zrrraa/X-Focus/dependencies/images/login_1.png

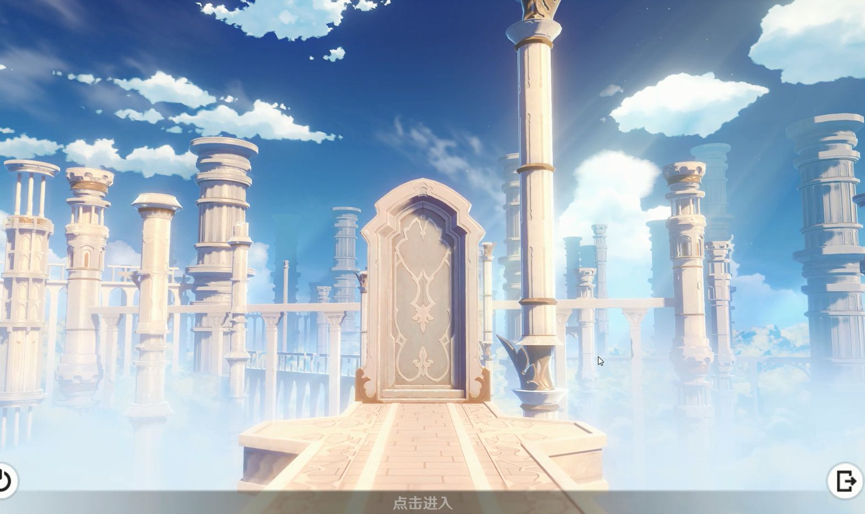
dependencies/images/login_1.png
