zrrraa/X-Focus/dependencies/images/lzt1_touxiang.png

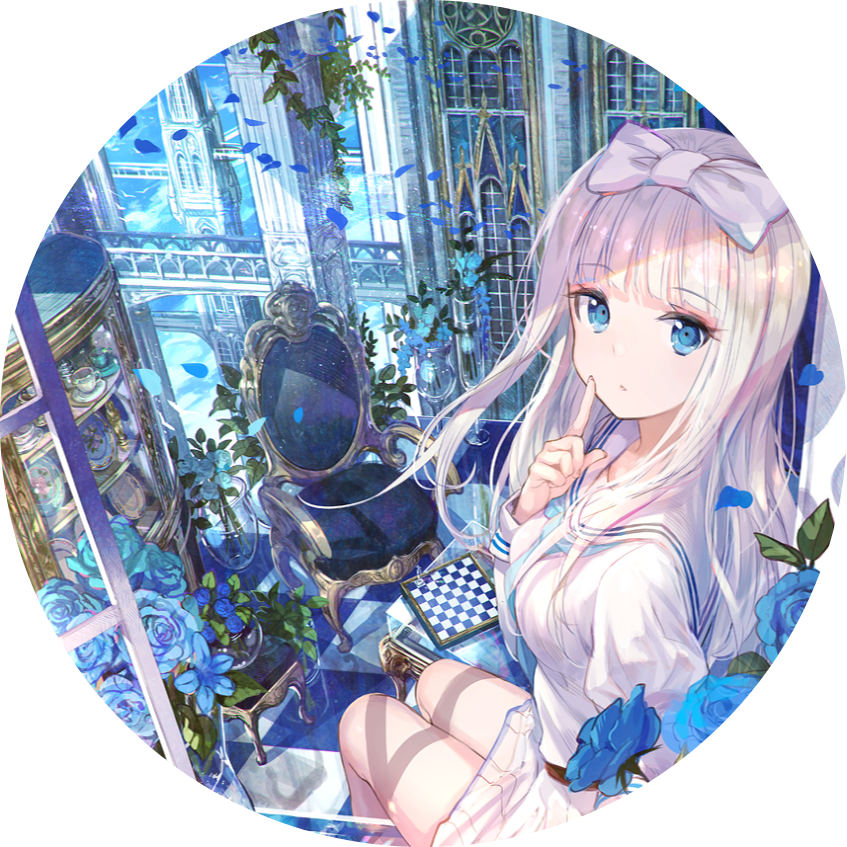
dependencies/images/lzt1_touxiang.png
