zrrraa/X-Focus/dependencies/images/signup.jpg

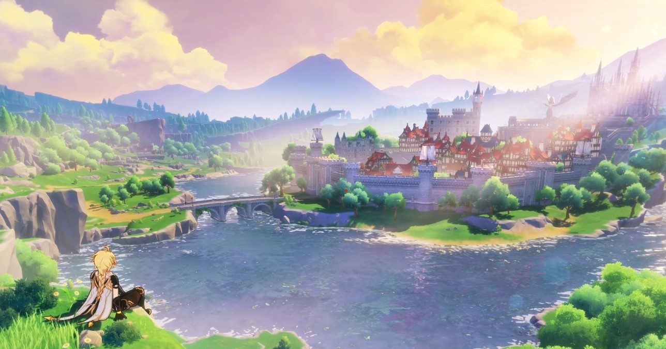
dependencies/images/signup.jpg
