zrrraa/X-Focus/dependencies/images/zrraaa_touxiang.png

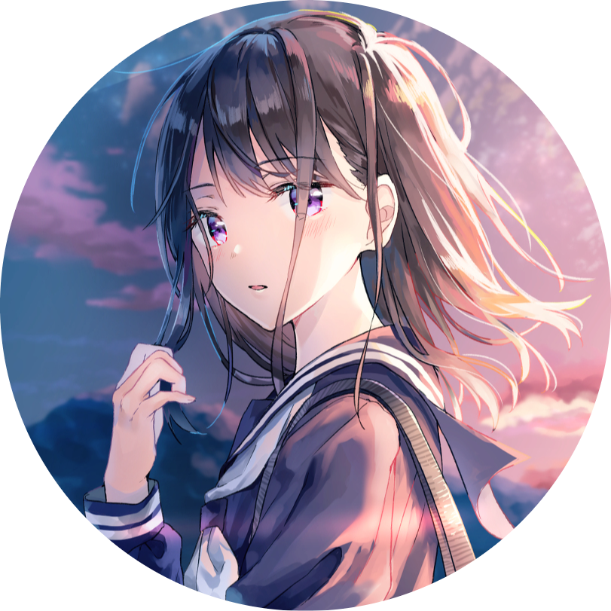
dependencies/images/zrraaa_touxiang.png
