zrrraa/X-Focus/SVMImageClassification/photo2/0/0.jpg

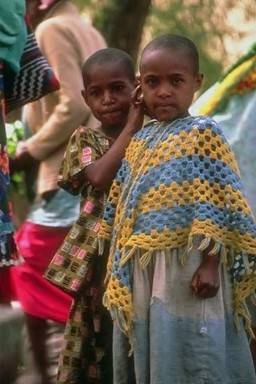
SVMImageClassification/photo2/0/0.jpg
