zrrraa/X-Focus/SVMImageClassification/photo2/0/3.jpg

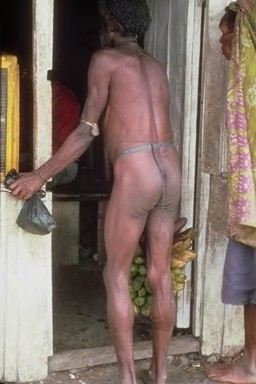
SVMImageClassification/photo2/0/3.jpg
