zrrraa/X-Focus/SVMImageClassification/photo2/0/6.jpg

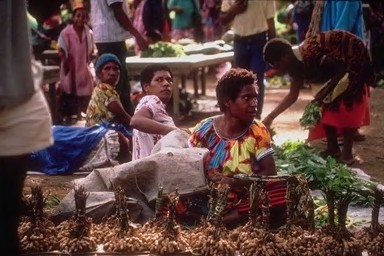
SVMImageClassification/photo2/0/6.jpg
