zrrraa/X-Focus/SVMImageClassification/photo2/0/7.jpg

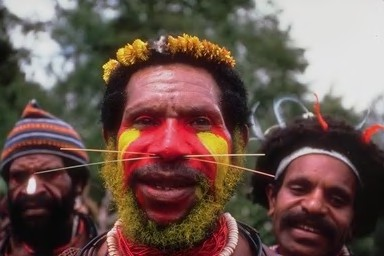
SVMImageClassification/photo2/0/7.jpg
