zrrraa/X-Focus/SVMImageClassification/photo2/0/9.jpg

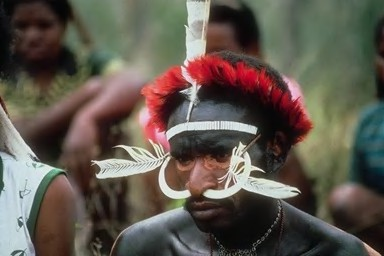
SVMImageClassification/photo2/0/9.jpg
