zrrraa/X-Focus/SVMImageClassification/photo2/0/15.jpg

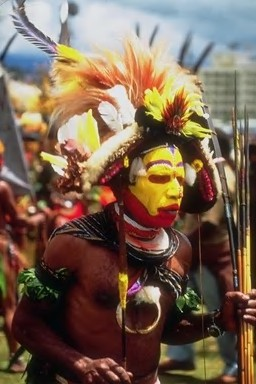
SVMImageClassification/photo2/0/15.jpg
