zrrraa/X-Focus/SVMImageClassification/photo2/0/25.jpg

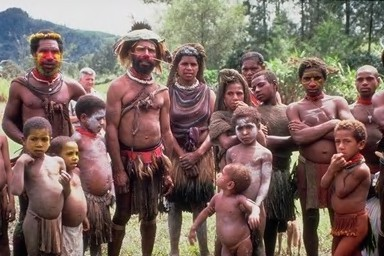
SVMImageClassification/photo2/0/25.jpg
