zrrraa/X-Focus/SVMImageClassification/photo2/0/32.jpg

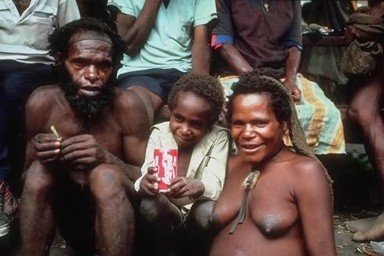
SVMImageClassification/photo2/0/32.jpg
