zrrraa/X-Focus/SVMImageClassification/photo2/0/33.jpg

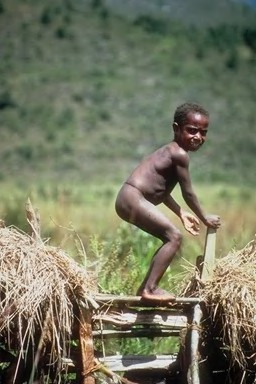
SVMImageClassification/photo2/0/33.jpg
