zrrraa/X-Focus/SVMImageClassification/photo2/0/38.jpg

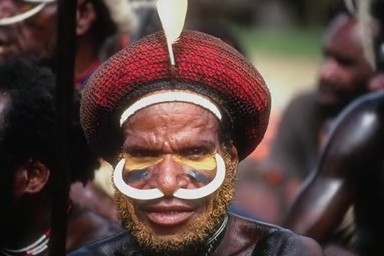
SVMImageClassification/photo2/0/38.jpg
