zrrraa/X-Focus/SVMImageClassification/photo2/0/42.jpg

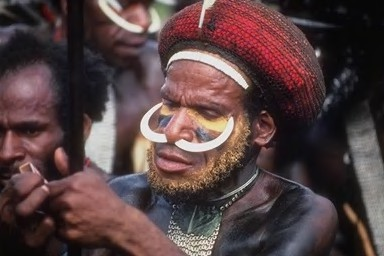
SVMImageClassification/photo2/0/42.jpg
