zrrraa/X-Focus/SVMImageClassification/photo2/0/44.jpg

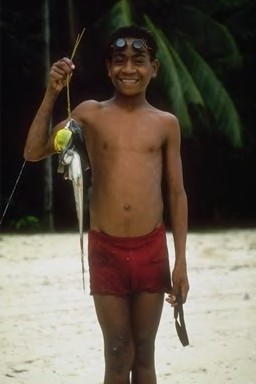
SVMImageClassification/photo2/0/44.jpg
