zrrraa/X-Focus/SVMImageClassification/photo2/0/46.jpg

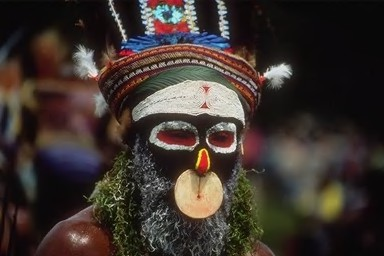
SVMImageClassification/photo2/0/46.jpg
