zrrraa/X-Focus/SVMImageClassification/photo2/0/49.jpg

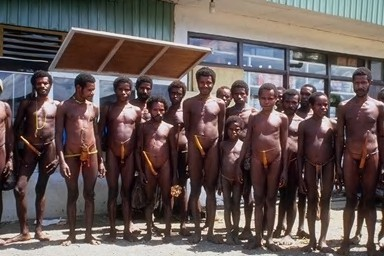
SVMImageClassification/photo2/0/49.jpg
