zrrraa/X-Focus/SVMImageClassification/photo2/0/62.jpg

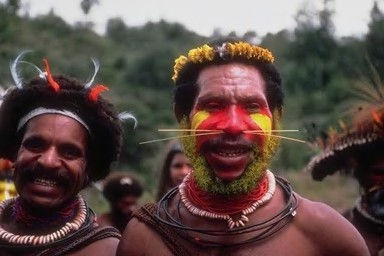
SVMImageClassification/photo2/0/62.jpg
