zrrraa/X-Focus/SVMImageClassification/photo2/0/65.jpg

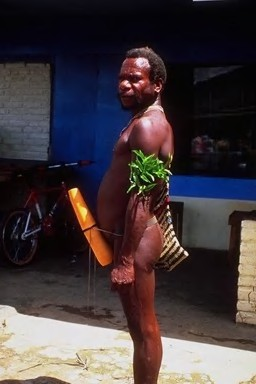
SVMImageClassification/photo2/0/65.jpg
