zrrraa/X-Focus/SVMImageClassification/photo2/0/79.jpg

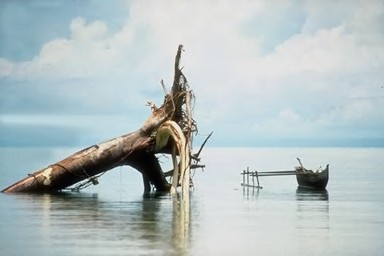
SVMImageClassification/photo2/0/79.jpg
