zrrraa/X-Focus/SVMImageClassification/photo2/0/83.jpg

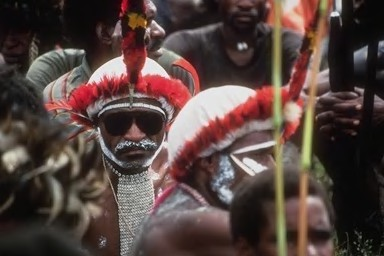
SVMImageClassification/photo2/0/83.jpg
