zrrraa/X-Focus/SVMImageClassification/photo2/0/86.jpg

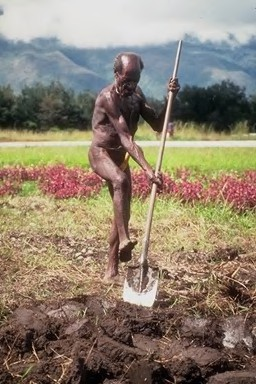
SVMImageClassification/photo2/0/86.jpg
