zrrraa/X-Focus/SVMImageClassification/photo2/0/90.jpg

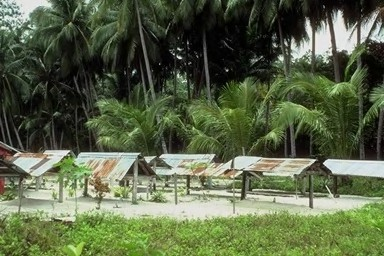
SVMImageClassification/photo2/0/90.jpg
