zrrraa/X-Focus/SVMImageClassification/photo2/0/97.jpg

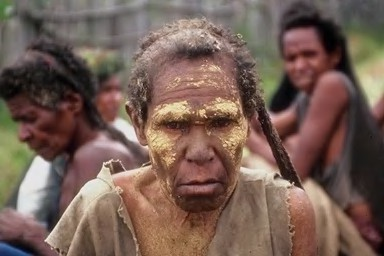
SVMImageClassification/photo2/0/97.jpg
