zrrraa/X-Focus/SVMImageClassification/photo2/1/100.jpg

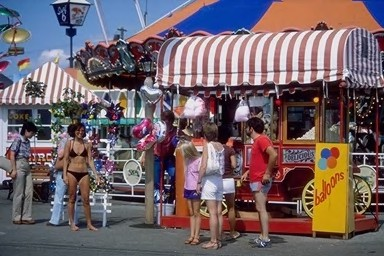
SVMImageClassification/photo2/1/100.jpg
