zrrraa/X-Focus/SVMImageClassification/photo2/1/103.jpg

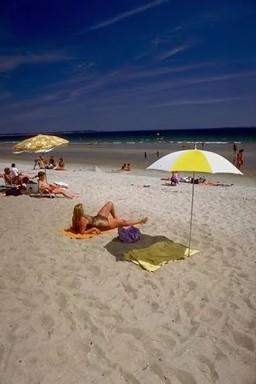
SVMImageClassification/photo2/1/103.jpg
