zrrraa/X-Focus/SVMImageClassification/photo2/1/105.jpg

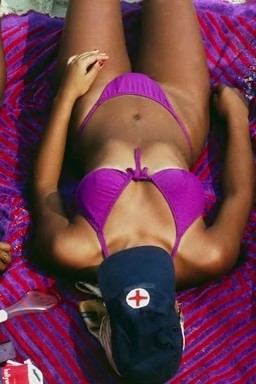
SVMImageClassification/photo2/1/105.jpg
