zrrraa/X-Focus/SVMImageClassification/photo2/1/115.jpg

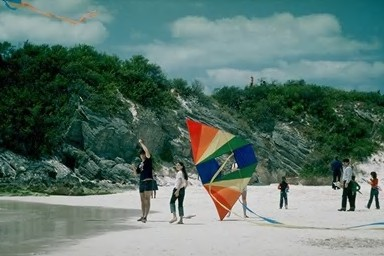
SVMImageClassification/photo2/1/115.jpg
