zrrraa/X-Focus/SVMImageClassification/photo2/1/118.jpg

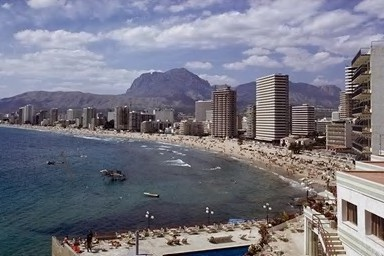
SVMImageClassification/photo2/1/118.jpg
