zrrraa/X-Focus/SVMImageClassification/photo2/1/129.jpg

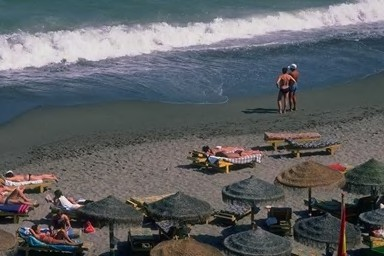
SVMImageClassification/photo2/1/129.jpg
