zrrraa/X-Focus/SVMImageClassification/photo2/1/141.jpg

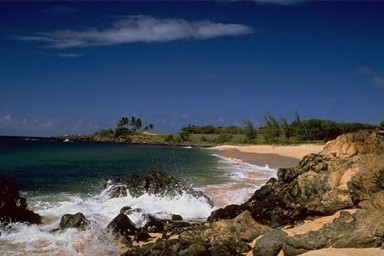
SVMImageClassification/photo2/1/141.jpg
