zrrraa/X-Focus/SVMImageClassification/photo2/1/146.jpg

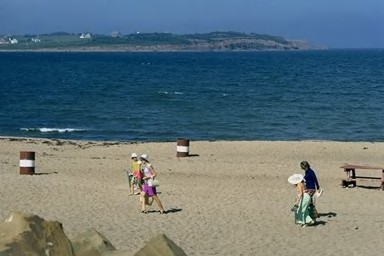
SVMImageClassification/photo2/1/146.jpg
