zrrraa/X-Focus/SVMImageClassification/photo2/1/149.jpg

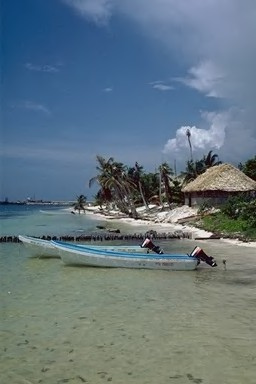
SVMImageClassification/photo2/1/149.jpg
