zrrraa/X-Focus/SVMImageClassification/photo2/1/160.jpg

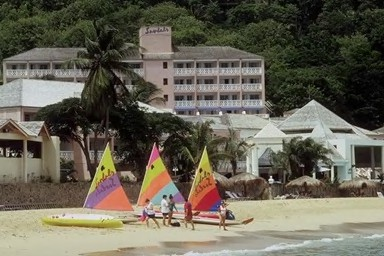
SVMImageClassification/photo2/1/160.jpg
