zrrraa/X-Focus/SVMImageClassification/photo2/1/161.jpg

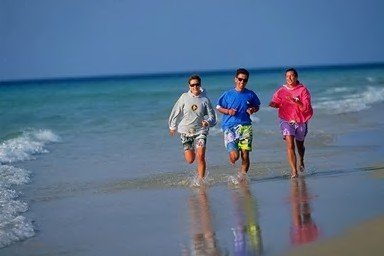
SVMImageClassification/photo2/1/161.jpg
