zrrraa/X-Focus/SVMImageClassification/photo2/1/162.jpg

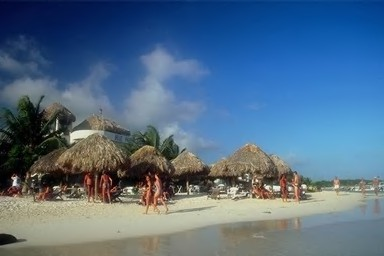
SVMImageClassification/photo2/1/162.jpg
