zrrraa/X-Focus/SVMImageClassification/photo2/1/167.jpg

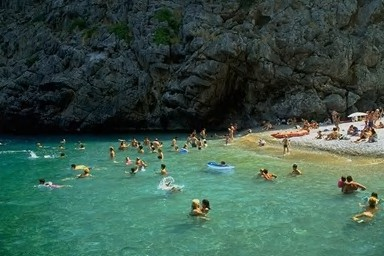
SVMImageClassification/photo2/1/167.jpg
