zrrraa/X-Focus/SVMImageClassification/photo2/1/170.jpg

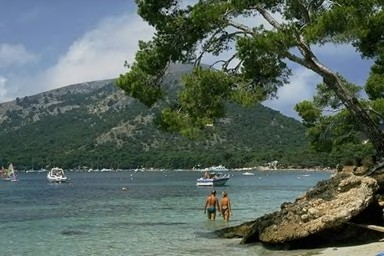
SVMImageClassification/photo2/1/170.jpg
