zrrraa/X-Focus/SVMImageClassification/photo2/1/172.jpg

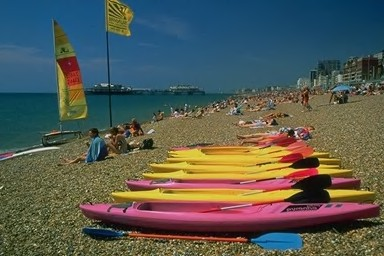
SVMImageClassification/photo2/1/172.jpg
