zrrraa/X-Focus/SVMImageClassification/photo2/1/175.jpg

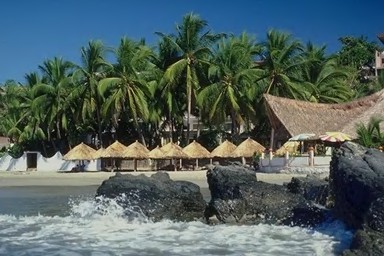
SVMImageClassification/photo2/1/175.jpg
