zrrraa/X-Focus/SVMImageClassification/photo2/1/178.jpg

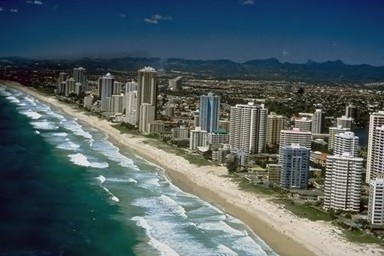
SVMImageClassification/photo2/1/178.jpg
