zrrraa/X-Focus/SVMImageClassification/photo2/1/180.jpg

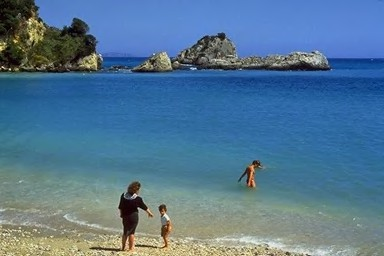
SVMImageClassification/photo2/1/180.jpg
