zrrraa/X-Focus/SVMImageClassification/photo2/1/187.jpg

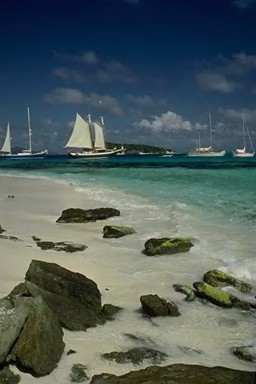
SVMImageClassification/photo2/1/187.jpg
