zrrraa/X-Focus/SVMImageClassification/photo2/1/194.jpg

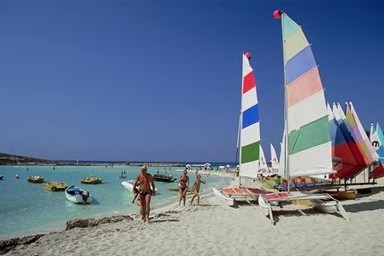
SVMImageClassification/photo2/1/194.jpg
