zrrraa/X-Focus/SVMImageClassification/photo2/2/202.jpg

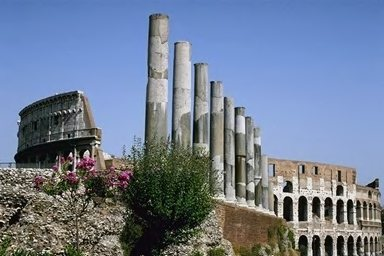
SVMImageClassification/photo2/2/202.jpg
