zrrraa/X-Focus/SVMImageClassification/photo2/2/207.jpg

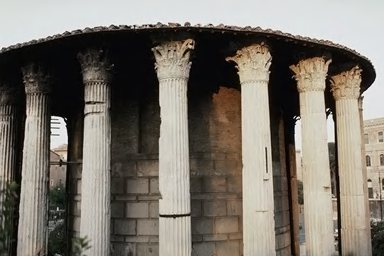
SVMImageClassification/photo2/2/207.jpg
