zrrraa/X-Focus/SVMImageClassification/photo2/2/211.jpg

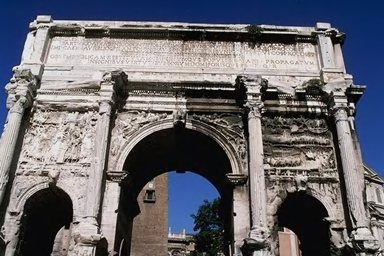
SVMImageClassification/photo2/2/211.jpg
