zrrraa/X-Focus/SVMImageClassification/photo2/2/225.jpg

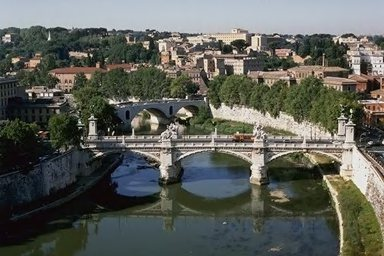
SVMImageClassification/photo2/2/225.jpg
