zrrraa/X-Focus/SVMImageClassification/photo2/2/231.jpg

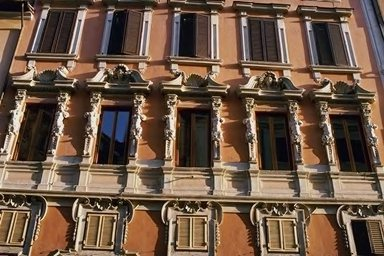
SVMImageClassification/photo2/2/231.jpg
