zrrraa/X-Focus/SVMImageClassification/photo2/2/239.jpg

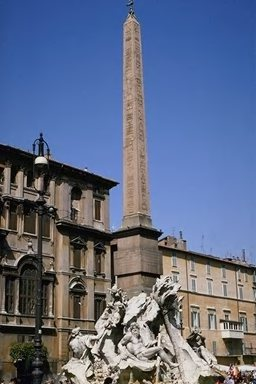
SVMImageClassification/photo2/2/239.jpg
