zrrraa/X-Focus/SVMImageClassification/photo2/2/246.jpg

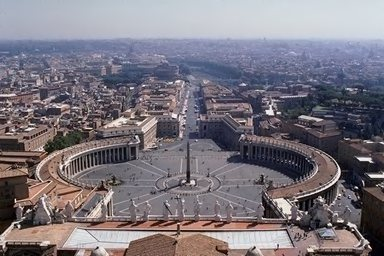
SVMImageClassification/photo2/2/246.jpg
