zrrraa/X-Focus/SVMImageClassification/photo2/2/264.jpg

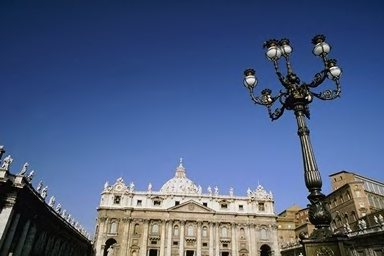
SVMImageClassification/photo2/2/264.jpg
