zrrraa/X-Focus/SVMImageClassification/photo2/2/267.jpg

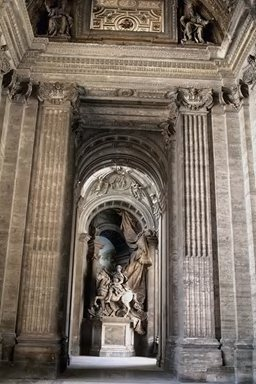
SVMImageClassification/photo2/2/267.jpg
