zrrraa/X-Focus/SVMImageClassification/photo2/2/278.jpg

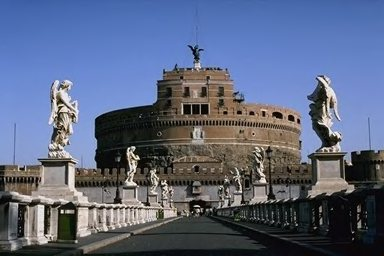
SVMImageClassification/photo2/2/278.jpg
