zrrraa/X-Focus/SVMImageClassification/photo2/3/300.jpg

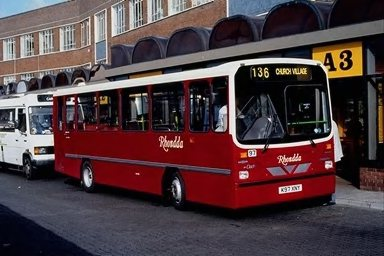
SVMImageClassification/photo2/3/300.jpg
