zrrraa/X-Focus/SVMImageClassification/photo2/3/312.jpg

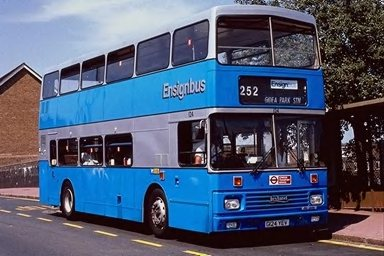
SVMImageClassification/photo2/3/312.jpg
