zrrraa/X-Focus/SVMImageClassification/photo2/3/313.jpg

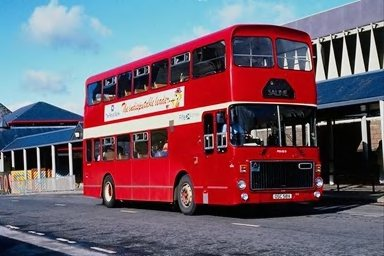
SVMImageClassification/photo2/3/313.jpg
