zrrraa/X-Focus/SVMImageClassification/photo2/3/318.jpg

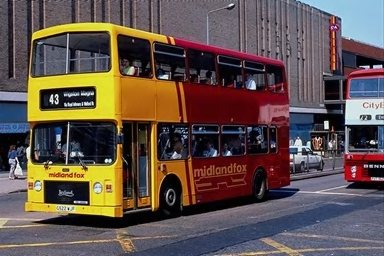
SVMImageClassification/photo2/3/318.jpg
