zrrraa/X-Focus/SVMImageClassification/photo2/3/319.jpg

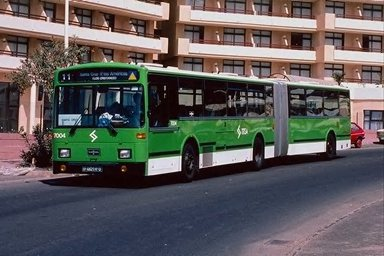
SVMImageClassification/photo2/3/319.jpg
