zrrraa/X-Focus/SVMImageClassification/photo2/3/320.jpg

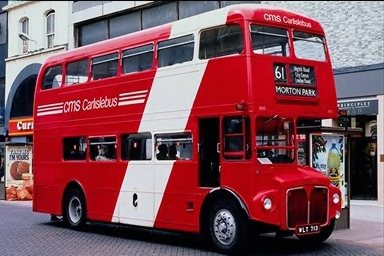
SVMImageClassification/photo2/3/320.jpg
