zrrraa/X-Focus/SVMImageClassification/photo2/3/337.jpg

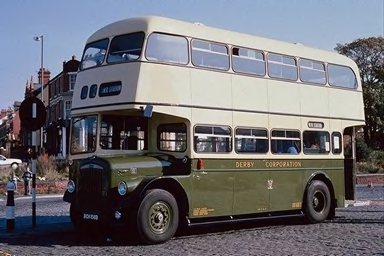
SVMImageClassification/photo2/3/337.jpg
