zrrraa/X-Focus/SVMImageClassification/photo2/3/340.jpg

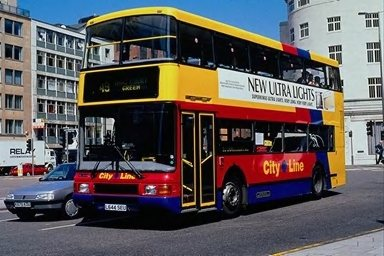
SVMImageClassification/photo2/3/340.jpg
