zrrraa/X-Focus/SVMImageClassification/photo2/3/342.jpg

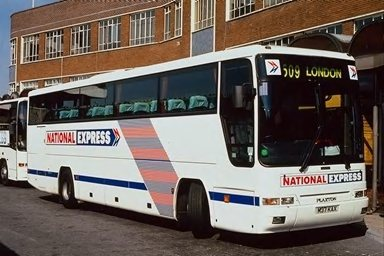
SVMImageClassification/photo2/3/342.jpg
