zrrraa/X-Focus/SVMImageClassification/photo2/3/356.jpg

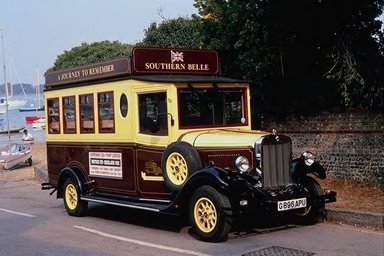
SVMImageClassification/photo2/3/356.jpg
