zrrraa/X-Focus/SVMImageClassification/photo2/3/363.jpg

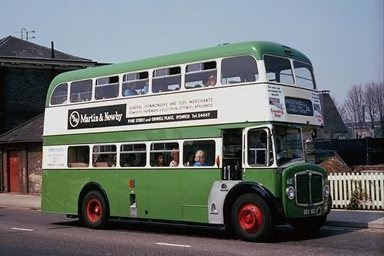
SVMImageClassification/photo2/3/363.jpg
