zrrraa/X-Focus/SVMImageClassification/photo2/3/382.jpg

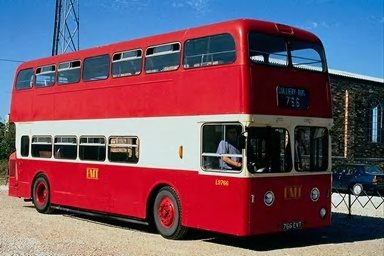
SVMImageClassification/photo2/3/382.jpg
