zrrraa/X-Focus/SVMImageClassification/photo2/3/388.jpg

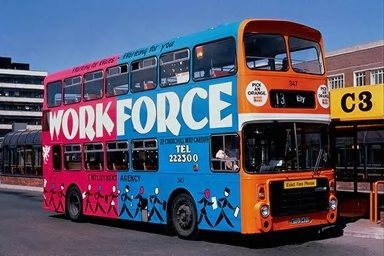
SVMImageClassification/photo2/3/388.jpg
