zrrraa/X-Focus/SVMImageClassification/photo2/3/393.jpg

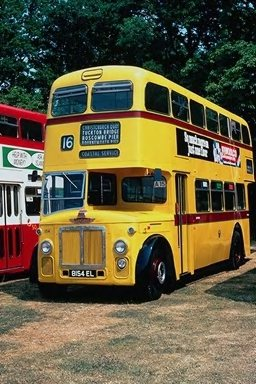
SVMImageClassification/photo2/3/393.jpg
