zrrraa/X-Focus/SVMImageClassification/photo2/4/403.jpg

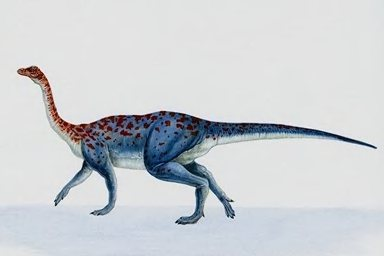
SVMImageClassification/photo2/4/403.jpg
