zrrraa/X-Focus/SVMImageClassification/photo2/4/406.jpg

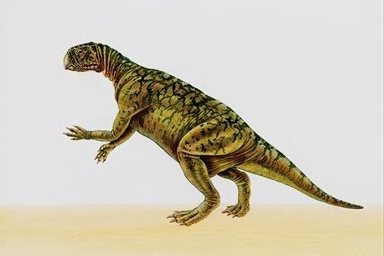
SVMImageClassification/photo2/4/406.jpg
