zrrraa/X-Focus/SVMImageClassification/photo2/4/411.jpg

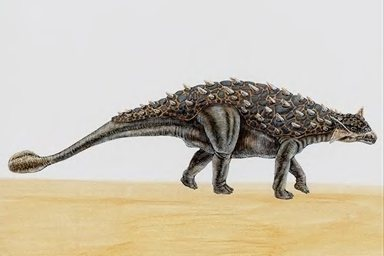
SVMImageClassification/photo2/4/411.jpg
