zrrraa/X-Focus/SVMImageClassification/photo2/4/413.jpg

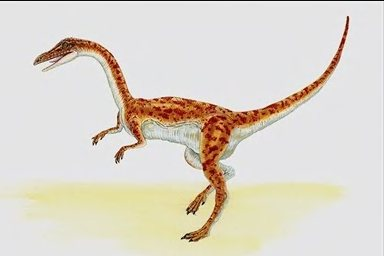
SVMImageClassification/photo2/4/413.jpg
