zrrraa/X-Focus/SVMImageClassification/photo2/4/423.jpg

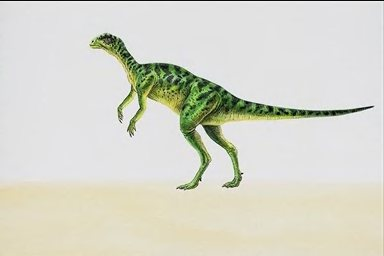
SVMImageClassification/photo2/4/423.jpg
