zrrraa/X-Focus/SVMImageClassification/photo2/4/424.jpg

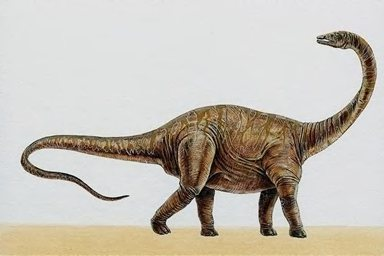
SVMImageClassification/photo2/4/424.jpg
