zrrraa/X-Focus/SVMImageClassification/photo2/4/426.jpg

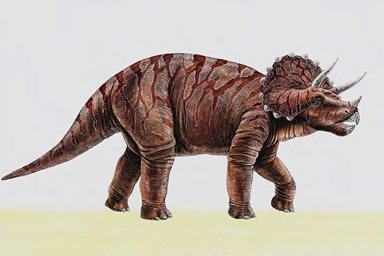
SVMImageClassification/photo2/4/426.jpg
