zrrraa/X-Focus/SVMImageClassification/photo2/4/437.jpg

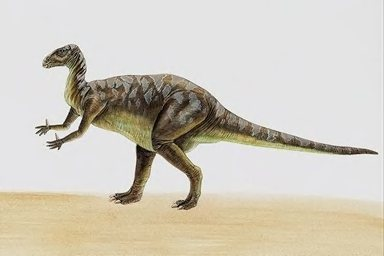
SVMImageClassification/photo2/4/437.jpg
