zrrraa/X-Focus/SVMImageClassification/photo2/4/442.jpg

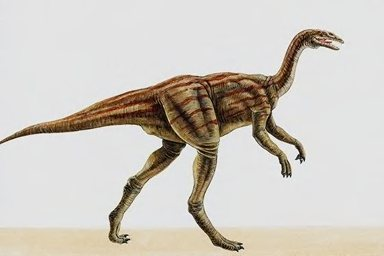
SVMImageClassification/photo2/4/442.jpg
