zrrraa/X-Focus/SVMImageClassification/photo2/4/444.jpg

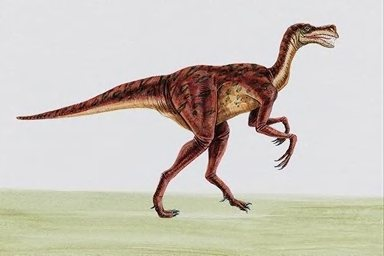
SVMImageClassification/photo2/4/444.jpg
