zrrraa/X-Focus/SVMImageClassification/photo2/4/446.jpg

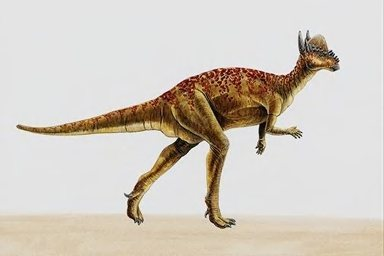
SVMImageClassification/photo2/4/446.jpg
