zrrraa/X-Focus/SVMImageClassification/photo2/4/447.jpg

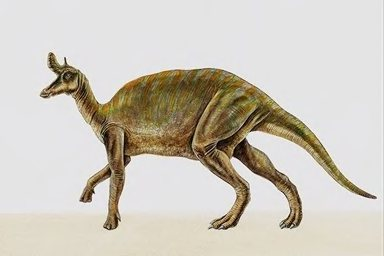
SVMImageClassification/photo2/4/447.jpg
