zrrraa/X-Focus/SVMImageClassification/photo2/4/449.jpg

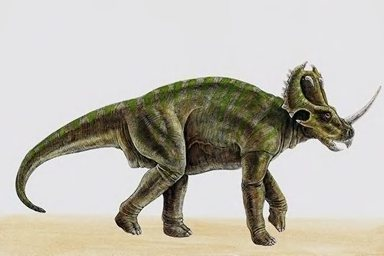
SVMImageClassification/photo2/4/449.jpg
