zrrraa/X-Focus/SVMImageClassification/photo2/4/460.jpg

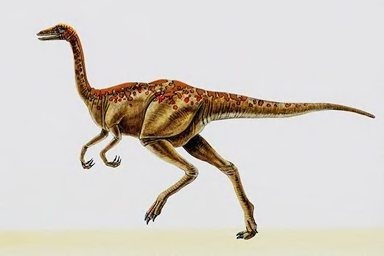
SVMImageClassification/photo2/4/460.jpg
