zrrraa/X-Focus/SVMImageClassification/photo2/4/462.jpg

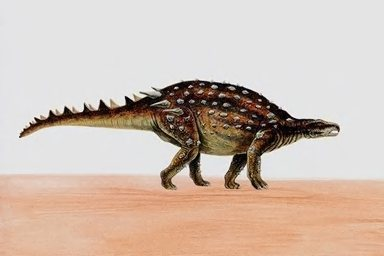
SVMImageClassification/photo2/4/462.jpg
