zrrraa/X-Focus/SVMImageClassification/photo2/4/463.jpg

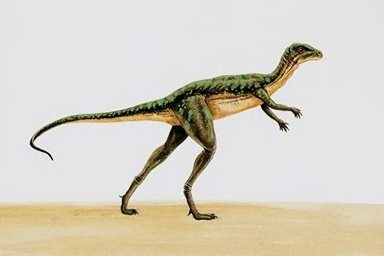
SVMImageClassification/photo2/4/463.jpg
