zrrraa/X-Focus/SVMImageClassification/photo2/4/467.jpg

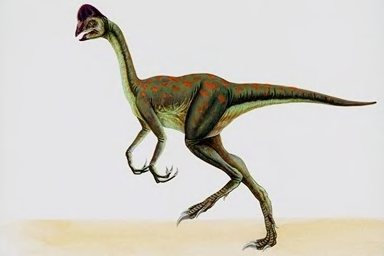
SVMImageClassification/photo2/4/467.jpg
