zrrraa/X-Focus/SVMImageClassification/photo2/4/475.jpg

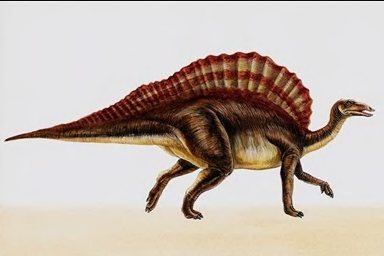
SVMImageClassification/photo2/4/475.jpg
