zrrraa/X-Focus/SVMImageClassification/photo2/4/477.jpg

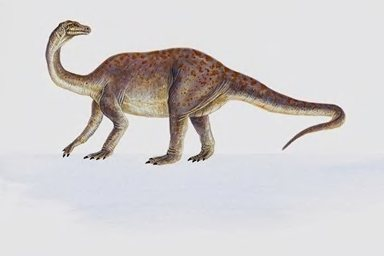
SVMImageClassification/photo2/4/477.jpg
