zrrraa/X-Focus/SVMImageClassification/photo2/4/480.jpg

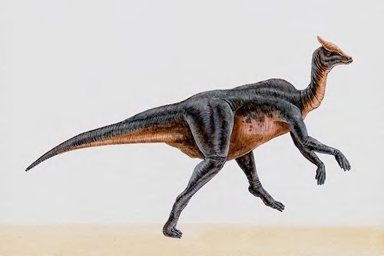
SVMImageClassification/photo2/4/480.jpg
