zrrraa/X-Focus/SVMImageClassification/photo2/4/482.jpg

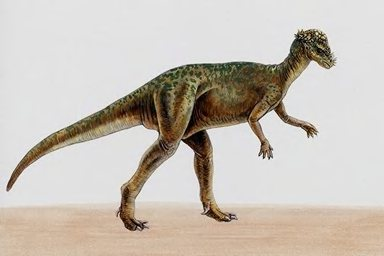
SVMImageClassification/photo2/4/482.jpg
