zrrraa/X-Focus/SVMImageClassification/photo2/4/483.jpg

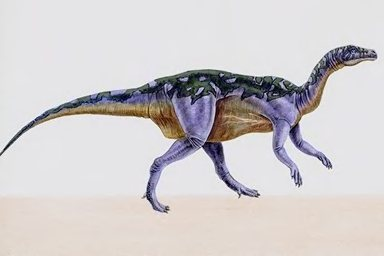
SVMImageClassification/photo2/4/483.jpg
