zrrraa/X-Focus/SVMImageClassification/photo2/4/485.jpg

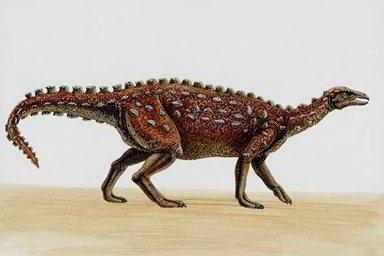
SVMImageClassification/photo2/4/485.jpg
