zrrraa/X-Focus/SVMImageClassification/photo2/4/486.jpg

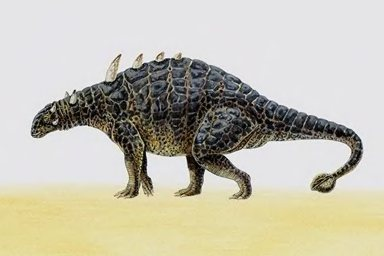
SVMImageClassification/photo2/4/486.jpg
