zrrraa/X-Focus/SVMImageClassification/photo2/4/494.jpg

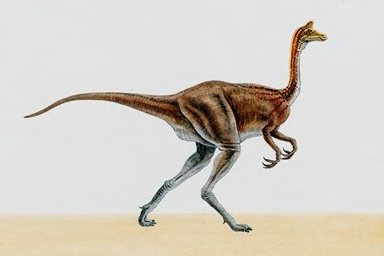
SVMImageClassification/photo2/4/494.jpg
