zrrraa/X-Focus/SVMImageClassification/photo2/4/499.jpg

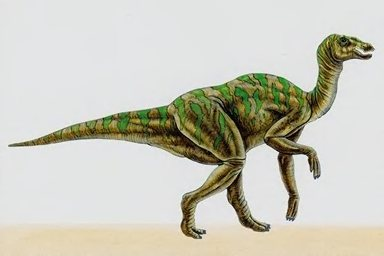
SVMImageClassification/photo2/4/499.jpg
