zrrraa/X-Focus/SVMImageClassification/photo2/5/506.jpg

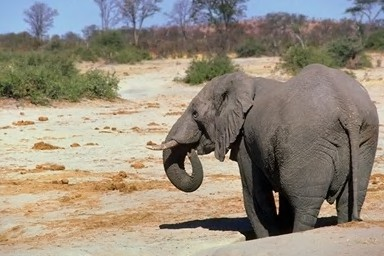
SVMImageClassification/photo2/5/506.jpg
