zrrraa/X-Focus/SVMImageClassification/photo2/5/523.jpg

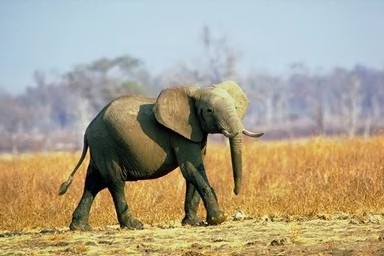
SVMImageClassification/photo2/5/523.jpg
