zrrraa/X-Focus/SVMImageClassification/photo2/5/533.jpg

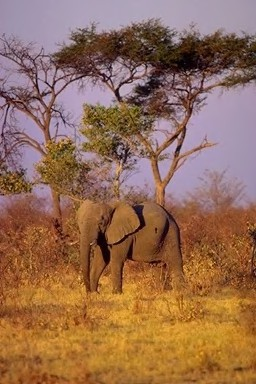
SVMImageClassification/photo2/5/533.jpg
