zrrraa/X-Focus/SVMImageClassification/photo2/5/543.jpg

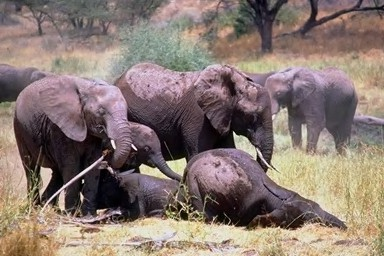
SVMImageClassification/photo2/5/543.jpg
