zrrraa/X-Focus/SVMImageClassification/photo2/5/545.jpg

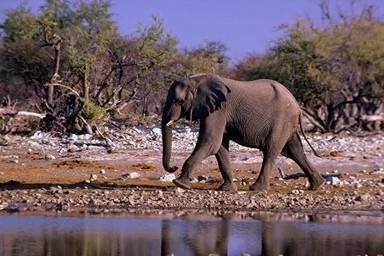
SVMImageClassification/photo2/5/545.jpg
