zrrraa/X-Focus/SVMImageClassification/photo2/5/547.jpg

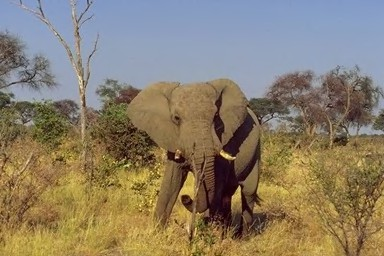
SVMImageClassification/photo2/5/547.jpg
