zrrraa/X-Focus/SVMImageClassification/photo2/5/548.jpg

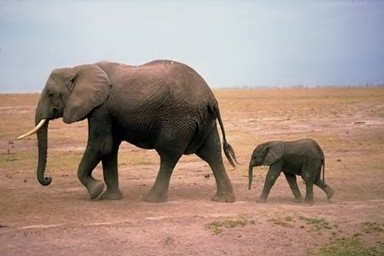
SVMImageClassification/photo2/5/548.jpg
