zrrraa/X-Focus/SVMImageClassification/photo2/5/550.jpg

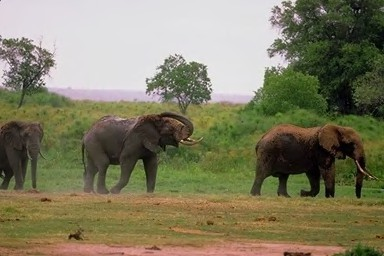
SVMImageClassification/photo2/5/550.jpg
