zrrraa/X-Focus/SVMImageClassification/photo2/5/566.jpg

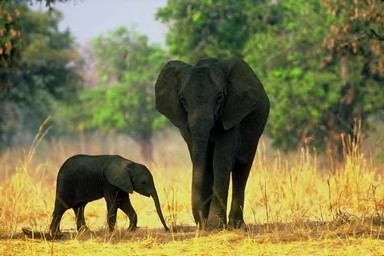
SVMImageClassification/photo2/5/566.jpg
