zrrraa/X-Focus/SVMImageClassification/photo2/5/571.jpg

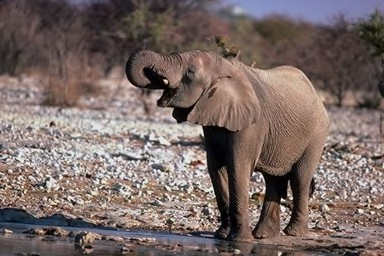
SVMImageClassification/photo2/5/571.jpg
