zrrraa/X-Focus/SVMImageClassification/photo2/5/574.jpg

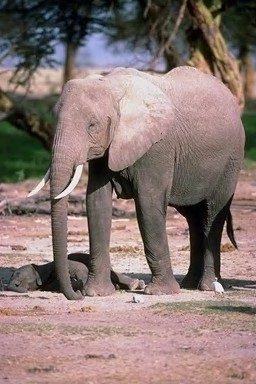
SVMImageClassification/photo2/5/574.jpg
