zrrraa/X-Focus/SVMImageClassification/photo2/5/576.jpg

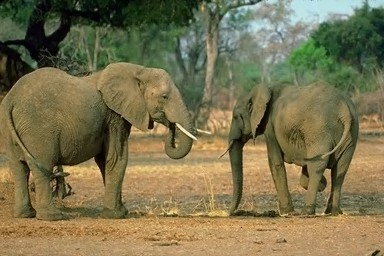
SVMImageClassification/photo2/5/576.jpg
