zrrraa/X-Focus/SVMImageClassification/photo2/5/577.jpg

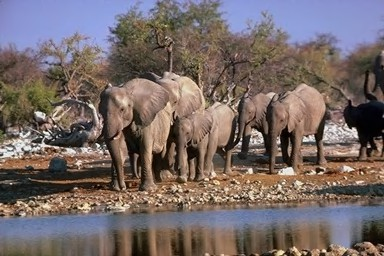
SVMImageClassification/photo2/5/577.jpg
