zrrraa/X-Focus/SVMImageClassification/photo2/5/593.jpg

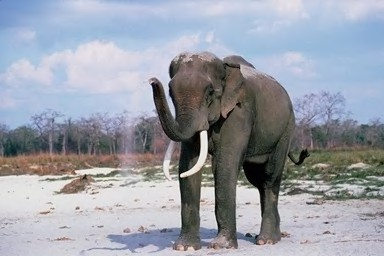
SVMImageClassification/photo2/5/593.jpg
