zrrraa/X-Focus/SVMImageClassification/photo2/5/596.jpg

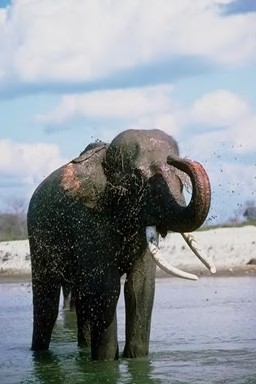
SVMImageClassification/photo2/5/596.jpg
