zrrraa/X-Focus/SVMImageClassification/photo2/6/600.jpg

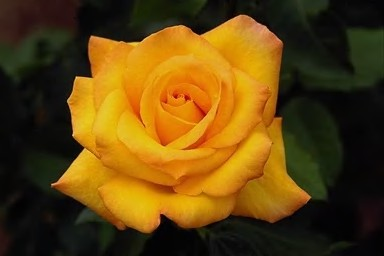
SVMImageClassification/photo2/6/600.jpg
