zrrraa/X-Focus/SVMImageClassification/photo2/6/608.jpg

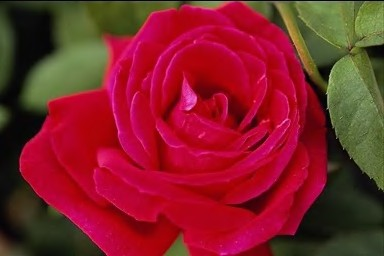
SVMImageClassification/photo2/6/608.jpg
