zrrraa/X-Focus/SVMImageClassification/photo2/6/616.jpg

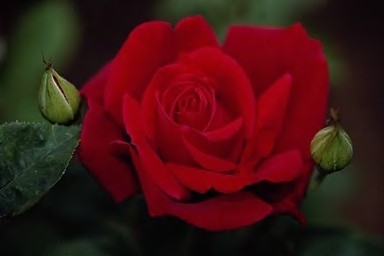
SVMImageClassification/photo2/6/616.jpg
