zrrraa/X-Focus/SVMImageClassification/photo2/6/623.jpg

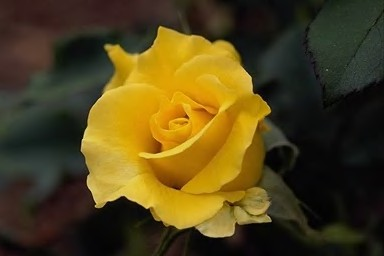
SVMImageClassification/photo2/6/623.jpg
