zrrraa/X-Focus/SVMImageClassification/photo2/6/625.jpg

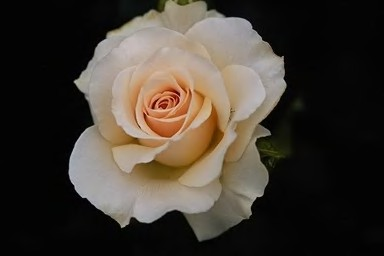
SVMImageClassification/photo2/6/625.jpg
