zrrraa/X-Focus/SVMImageClassification/photo2/6/630.jpg

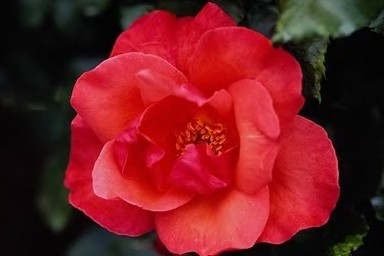
SVMImageClassification/photo2/6/630.jpg
