zrrraa/X-Focus/SVMImageClassification/photo2/6/631.jpg

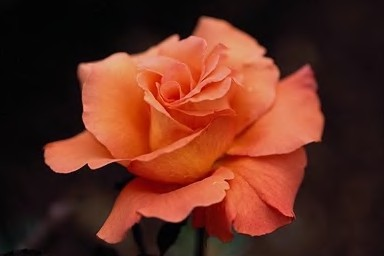
SVMImageClassification/photo2/6/631.jpg
