zrrraa/X-Focus/SVMImageClassification/photo2/6/632.jpg

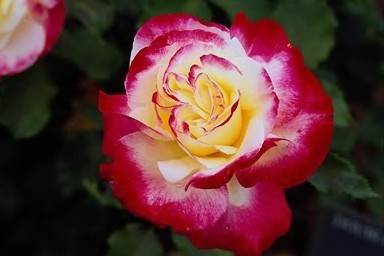
SVMImageClassification/photo2/6/632.jpg
