zrrraa/X-Focus/SVMImageClassification/photo2/6/643.jpg

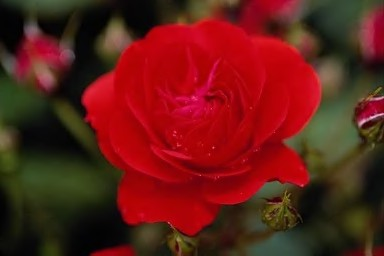
SVMImageClassification/photo2/6/643.jpg
