zrrraa/X-Focus/SVMImageClassification/photo2/6/645.jpg

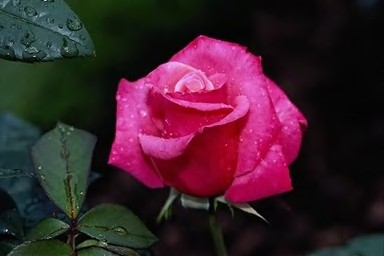
SVMImageClassification/photo2/6/645.jpg
