zrrraa/X-Focus/SVMImageClassification/photo2/6/648.jpg

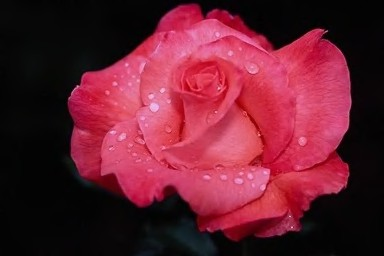
SVMImageClassification/photo2/6/648.jpg
