zrrraa/X-Focus/SVMImageClassification/photo2/6/651.jpg

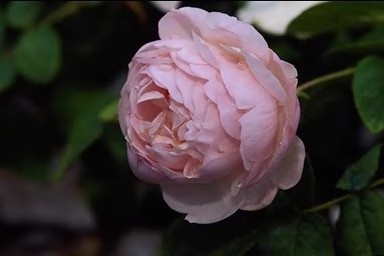
SVMImageClassification/photo2/6/651.jpg
