zrrraa/X-Focus/SVMImageClassification/photo2/6/655.jpg

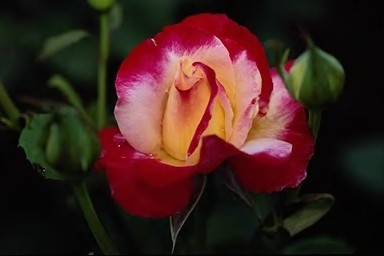
SVMImageClassification/photo2/6/655.jpg
