zrrraa/X-Focus/SVMImageClassification/photo2/6/657.jpg

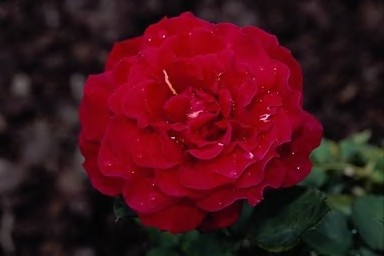
SVMImageClassification/photo2/6/657.jpg
