zrrraa/X-Focus/SVMImageClassification/photo2/6/659.jpg

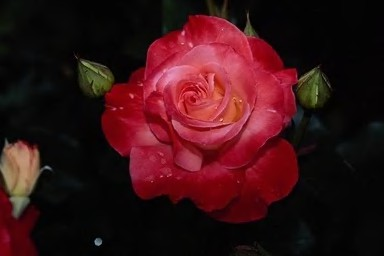
SVMImageClassification/photo2/6/659.jpg
