zrrraa/X-Focus/SVMImageClassification/photo2/6/661.jpg

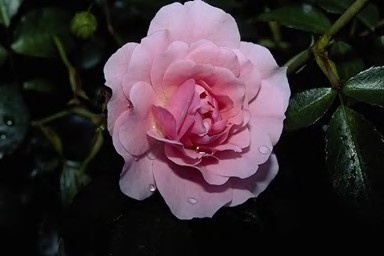
SVMImageClassification/photo2/6/661.jpg
