zrrraa/X-Focus/SVMImageClassification/photo2/6/663.jpg

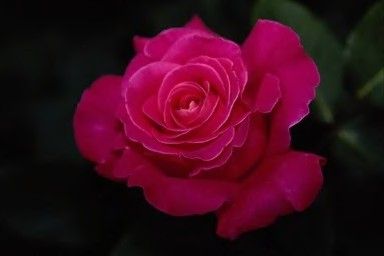
SVMImageClassification/photo2/6/663.jpg
