zrrraa/X-Focus/SVMImageClassification/photo2/6/670.jpg

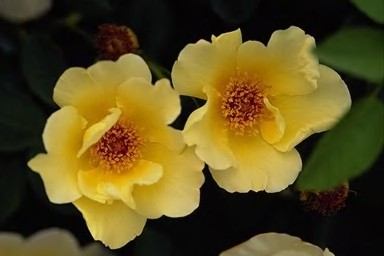
SVMImageClassification/photo2/6/670.jpg
