zrrraa/X-Focus/SVMImageClassification/photo2/6/685.jpg

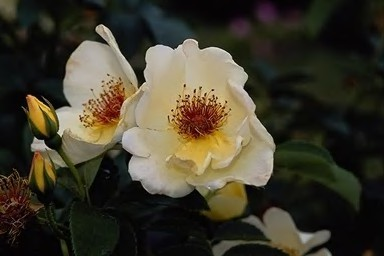
SVMImageClassification/photo2/6/685.jpg
