zrrraa/X-Focus/SVMImageClassification/photo2/6/690.jpg

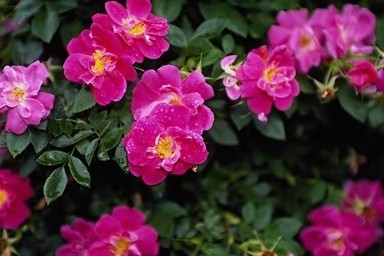
SVMImageClassification/photo2/6/690.jpg
