zrrraa/X-Focus/SVMImageClassification/photo2/7/700.jpg

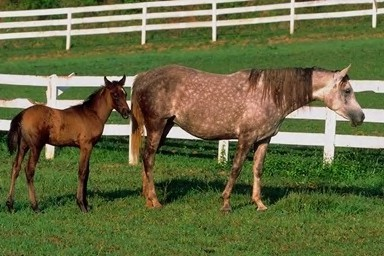
SVMImageClassification/photo2/7/700.jpg
