zrrraa/X-Focus/SVMImageClassification/photo2/7/709.jpg

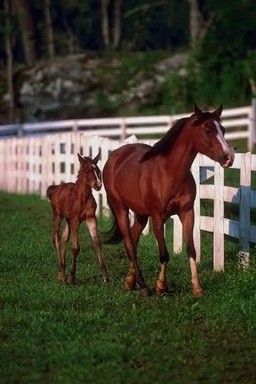
SVMImageClassification/photo2/7/709.jpg
