zrrraa/X-Focus/SVMImageClassification/photo2/7/724.jpg

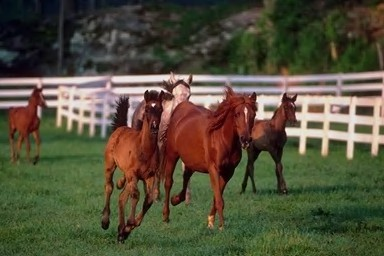
SVMImageClassification/photo2/7/724.jpg
