zrrraa/X-Focus/SVMImageClassification/photo2/7/727.jpg

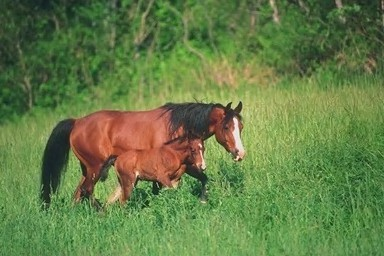
SVMImageClassification/photo2/7/727.jpg
