zrrraa/X-Focus/SVMImageClassification/photo2/7/729.jpg

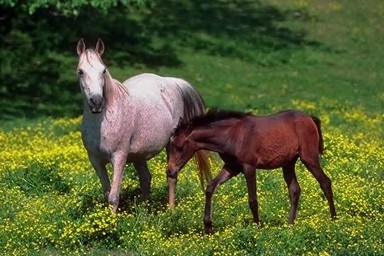
SVMImageClassification/photo2/7/729.jpg
