zrrraa/X-Focus/SVMImageClassification/photo2/7/746.jpg

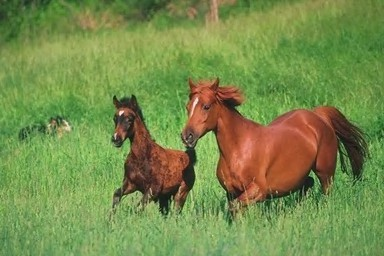
SVMImageClassification/photo2/7/746.jpg
