zrrraa/X-Focus/SVMImageClassification/photo2/7/751.jpg

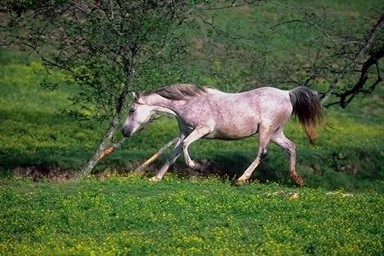
SVMImageClassification/photo2/7/751.jpg
