zrrraa/X-Focus/SVMImageClassification/photo2/7/771.jpg

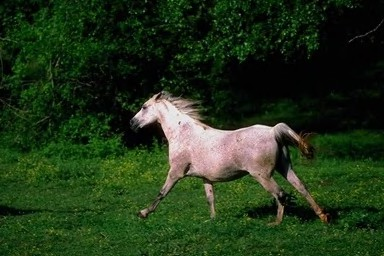
SVMImageClassification/photo2/7/771.jpg
