zrrraa/X-Focus/SVMImageClassification/photo2/7/784.jpg

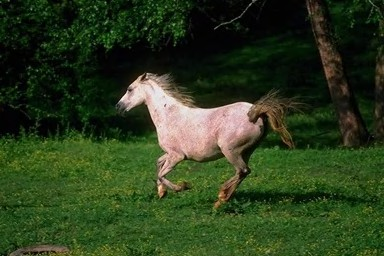
SVMImageClassification/photo2/7/784.jpg
