zrrraa/X-Focus/SVMImageClassification/photo2/8/803.jpg

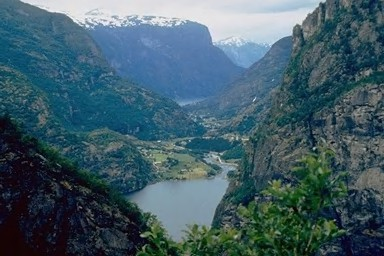
SVMImageClassification/photo2/8/803.jpg
