zrrraa/X-Focus/SVMImageClassification/photo2/8/814.jpg

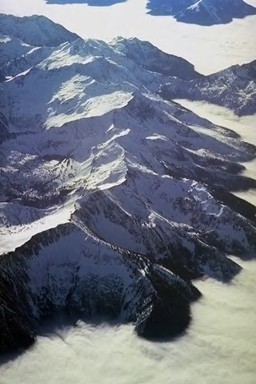
SVMImageClassification/photo2/8/814.jpg
