zrrraa/X-Focus/SVMImageClassification/photo2/8/830.jpg

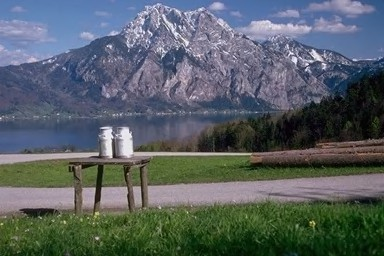
SVMImageClassification/photo2/8/830.jpg
