zrrraa/X-Focus/SVMImageClassification/photo2/8/840.jpg

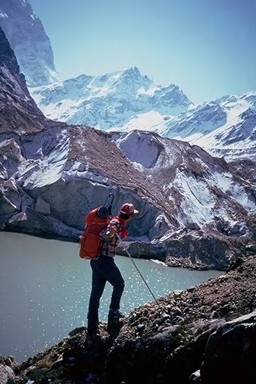
SVMImageClassification/photo2/8/840.jpg
