zrrraa/X-Focus/SVMImageClassification/photo2/8/847.jpg

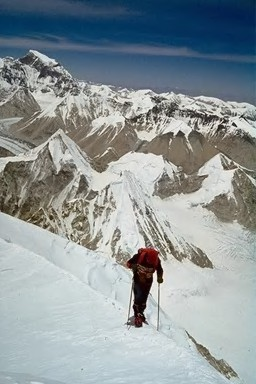
SVMImageClassification/photo2/8/847.jpg
