zrrraa/X-Focus/SVMImageClassification/photo2/8/857.jpg

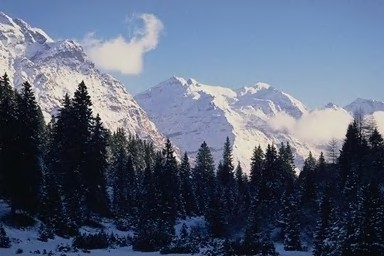
SVMImageClassification/photo2/8/857.jpg
