zrrraa/X-Focus/SVMImageClassification/photo2/8/862.jpg

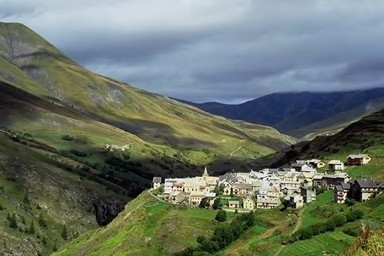
SVMImageClassification/photo2/8/862.jpg
