zrrraa/X-Focus/SVMImageClassification/photo2/8/865.jpg

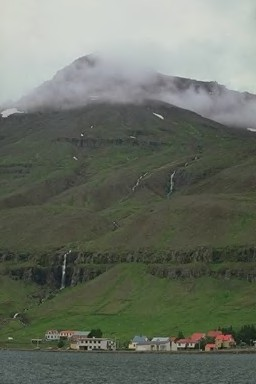
SVMImageClassification/photo2/8/865.jpg
