zrrraa/X-Focus/SVMImageClassification/photo2/8/874.jpg

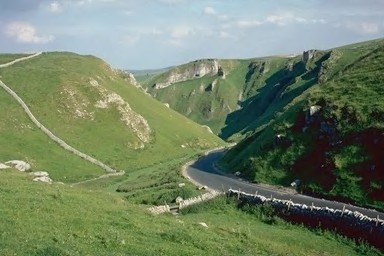
SVMImageClassification/photo2/8/874.jpg
