zrrraa/X-Focus/SVMImageClassification/photo2/8/879.jpg

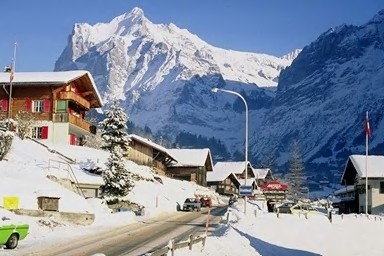
SVMImageClassification/photo2/8/879.jpg
