zrrraa/X-Focus/SVMImageClassification/photo2/8/885.jpg

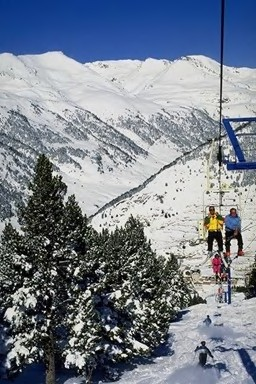
SVMImageClassification/photo2/8/885.jpg
