zrrraa/X-Focus/SVMImageClassification/photo2/8/886.jpg

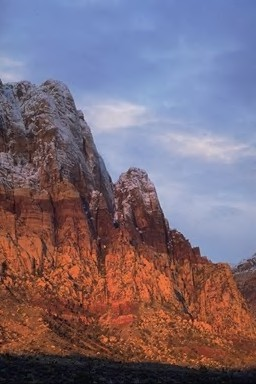
SVMImageClassification/photo2/8/886.jpg
