zrrraa/X-Focus/SVMImageClassification/photo2/9/902.jpg

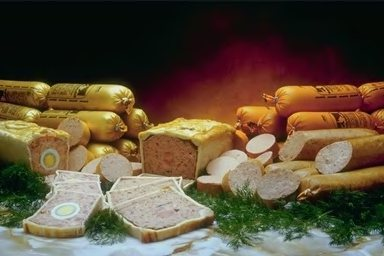
SVMImageClassification/photo2/9/902.jpg
