zrrraa/X-Focus/SVMImageClassification/photo2/9/911.jpg

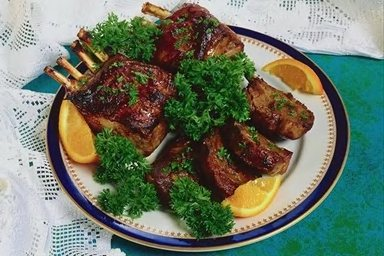
SVMImageClassification/photo2/9/911.jpg
