zrrraa/X-Focus/SVMImageClassification/photo2/9/915.jpg

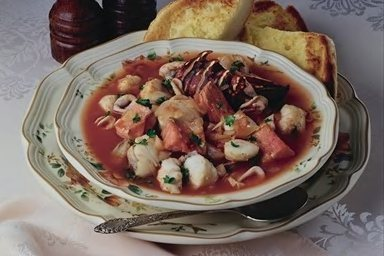
SVMImageClassification/photo2/9/915.jpg
