zrrraa/X-Focus/SVMImageClassification/photo2/9/936.jpg

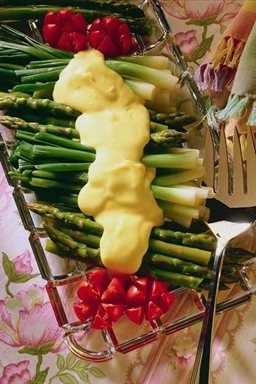
SVMImageClassification/photo2/9/936.jpg
