zrrraa/X-Focus/SVMImageClassification/photo2/9/956.jpg

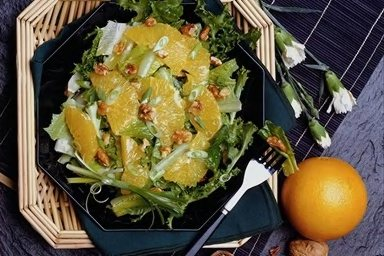
SVMImageClassification/photo2/9/956.jpg
