zrrraa/X-Focus/SVMImageClassification/photo2/9/957.jpg

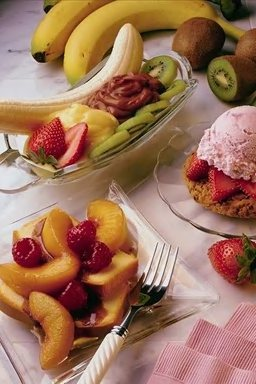
SVMImageClassification/photo2/9/957.jpg
