zrrraa/X-Focus/SVMImageClassification/photo2/9/979.jpg

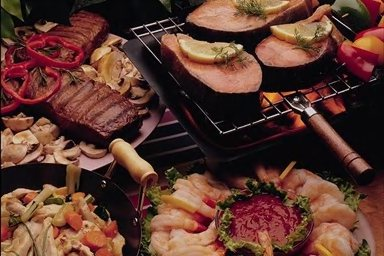
SVMImageClassification/photo2/9/979.jpg
