zrrraa/X-Focus/SVMImageClassification/photo2/9/986.jpg

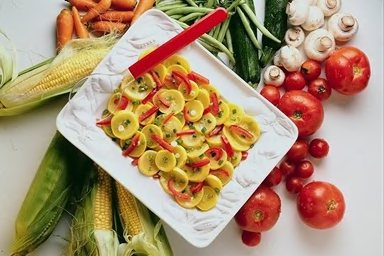
SVMImageClassification/photo2/9/986.jpg
