zrrraa/X-Focus/SVMImageClassification/photo2/9/987.jpg

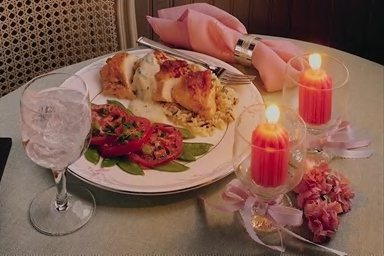
SVMImageClassification/photo2/9/987.jpg
