zrrraa/X-Focus/SVMImageClassification/photo3/0/3.png

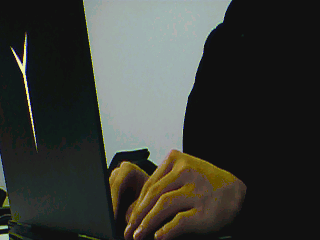
SVMImageClassification/photo3/0/3.png
