zrrraa/X-Focus/SVMImageClassification/photo3/1/100.png

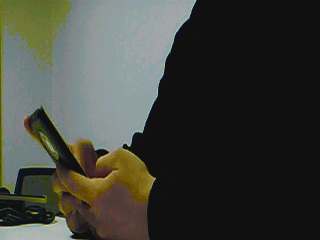
SVMImageClassification/photo3/1/100.png
