zrrraa/X-Focus/SVMImageClassification/photo3/1/112.png

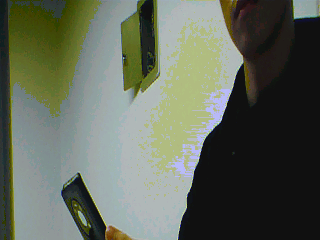
SVMImageClassification/photo3/1/112.png
