zrrraa/X-Focus/SVMImageClassification/photo3/2/209.png

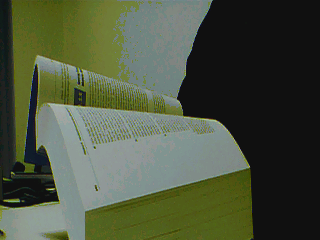
SVMImageClassification/photo3/2/209.png
