zrrraa/X-Focus/SVMImageClassification/photo3/2/212.png

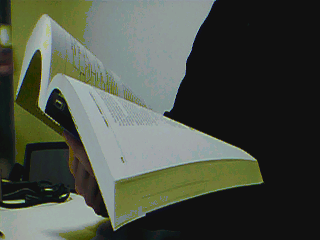
SVMImageClassification/photo3/2/212.png
