zrrraa/X-Focus/SVMImageClassification/photo3/3/300.png

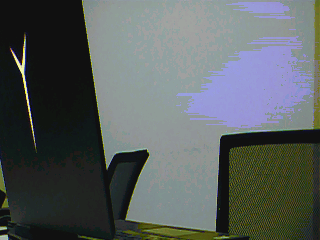
SVMImageClassification/photo3/3/300.png
