zrrraa/X-Focus/SVMImageClassification/photo/0/补焊00226_01条形缺陷2不分割__非原图.png

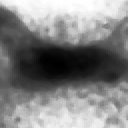
SVMImageClassification/photo/0/补焊00226_01条形缺陷2不分割__非原图.png
