zrrraa/X-Focus/SVMImageClassification/photo/0/补焊00229_01条形缺陷4不分割__非原图.png

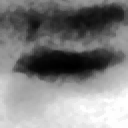
SVMImageClassification/photo/0/补焊00229_01条形缺陷4不分割__非原图.png
