zrrraa/X-Focus/SVMImageClassification/photo/0/补焊00267_01条形缺陷2分割_0_0_非原图.png

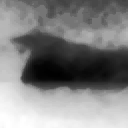
SVMImageClassification/photo/0/补焊00267_01条形缺陷2分割_0_0_非原图.png
