zrrraa/X-Focus/SVMImageClassification/photo/0/补焊00307_01条形缺陷3不分割__非原图.png

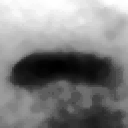
SVMImageClassification/photo/0/补焊00307_01条形缺陷3不分割__非原图.png
