zrrraa/X-Focus/SVMImageClassification/photo/0/补焊00308_01条形缺陷1分割_0_4_非原图.png

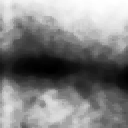
SVMImageClassification/photo/0/补焊00308_01条形缺陷1分割_0_4_非原图.png
