zrrraa/X-Focus/SVMImageClassification/photo/0/补焊00310_01条形缺陷3分割_0_1_非原图.png

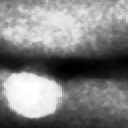
SVMImageClassification/photo/0/补焊00310_01条形缺陷3分割_0_1_非原图.png
