zrrraa/X-Focus/SVMImageClassification/photo/0/补焊00315_01条形缺陷9不分割__非原图.png

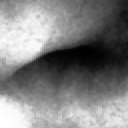
SVMImageClassification/photo/0/补焊00315_01条形缺陷9不分割__非原图.png
