zrrraa/X-Focus/SVMImageClassification/photo/0/补焊00355_01条形缺陷4分割_0_2_非原图.png

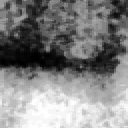
SVMImageClassification/photo/0/补焊00355_01条形缺陷4分割_0_2_非原图.png
