zrrraa/X-Focus/SVMImageClassification/photo/0/补焊00380_01条形缺陷1不分割__非原图.png

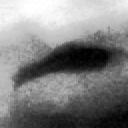
SVMImageClassification/photo/0/补焊00380_01条形缺陷1不分割__非原图.png
