zrrraa/X-Focus/SVMImageClassification/photo/1/补焊00365_01未焊透2分割_0_5_非原图.png

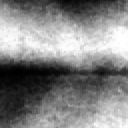
SVMImageClassification/photo/1/补焊00365_01未焊透2分割_0_5_非原图.png
