zrrraa/X-Focus/SVMImageClassification/photo/1/补焊00365_01未焊透3分割_0_3_非原图.png

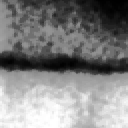
SVMImageClassification/photo/1/补焊00365_01未焊透3分割_0_3_非原图.png
