zrrraa/X-Focus/SVMImageClassification/photo/1/补焊00375_01未焊透4分割_0_5_非原图.png

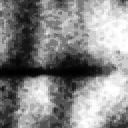
SVMImageClassification/photo/1/补焊00375_01未焊透4分割_0_5_非原图.png
