zrrraa/X-Focus/SVMImageClassification/photo/1/补焊00377_01未焊透2分割_0_1_非原图.png

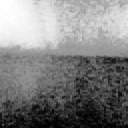
SVMImageClassification/photo/1/补焊00377_01未焊透2分割_0_1_非原图.png
