zrrraa/X-Focus/SVMImageClassification/photo/1/补焊00383_01未焊透1分割_0_1_非原图.png

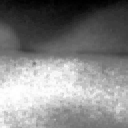
SVMImageClassification/photo/1/补焊00383_01未焊透1分割_0_1_非原图.png
