zrrraa/X-Focus/SVMImageClassification/photo/1/补焊00383_01未焊透3分割_0_4_非原图.png

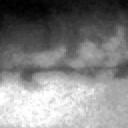
SVMImageClassification/photo/1/补焊00383_01未焊透3分割_0_4_非原图.png
