zrrraa/X-Focus/SVMImageClassification/photo/1/补焊00384_01未焊透1分割_0_14_非原图.png

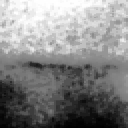
SVMImageClassification/photo/1/补焊00384_01未焊透1分割_0_14_非原图.png
