zrrraa/X-Focus/SVMImageClassification/photo/1/补焊00387_01未焊透3分割_0_2_非原图.png

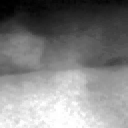
SVMImageClassification/photo/1/补焊00387_01未焊透3分割_0_2_非原图.png
