zrrraa/X-Focus/SVMImageClassification/photo/1/补焊00392_01未焊透1分割_0_11_非原图.png

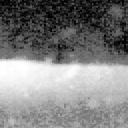
SVMImageClassification/photo/1/补焊00392_01未焊透1分割_0_11_非原图.png
