zrrraa/X-Focus/SVMImageClassification/photo/2/补焊00204_01未熔合3分割_0_3_非原图.png

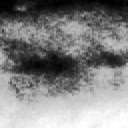
SVMImageClassification/photo/2/补焊00204_01未熔合3分割_0_3_非原图.png
