zrrraa/X-Focus/SVMImageClassification/photo/2/补焊00205_01未熔合2分割_0_3_非原图.png

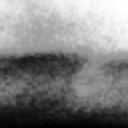
SVMImageClassification/photo/2/补焊00205_01未熔合2分割_0_3_非原图.png
