zrrraa/X-Focus/SVMImageClassification/photo/2/补焊00252_01未熔合2分割_0_1_非原图.png

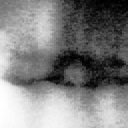
SVMImageClassification/photo/2/补焊00252_01未熔合2分割_0_1_非原图.png
