zrrraa/X-Focus/SVMImageClassification/photo/2/补焊00302_01未熔合2不分割__非原图.png

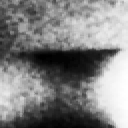
SVMImageClassification/photo/2/补焊00302_01未熔合2不分割__非原图.png
