zrrraa/X-Focus/SVMImageClassification/photo/2/补焊00302_01未熔合4不分割__非原图.png

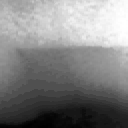
SVMImageClassification/photo/2/补焊00302_01未熔合4不分割__非原图.png
