zrrraa/X-Focus/SVMImageClassification/photo/2/补焊00344_02未熔合1分割_0_4_非原图.png

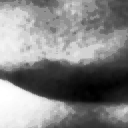
SVMImageClassification/photo/2/补焊00344_02未熔合1分割_0_4_非原图.png
