zrrraa/X-Focus/SVMImageClassification/photo/2/补焊00362_01未熔合4分割_0_0_非原图.png

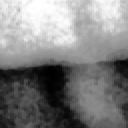
SVMImageClassification/photo/2/补焊00362_01未熔合4分割_0_0_非原图.png
