zrrraa/X-Focus/SVMImageClassification/photo/2/补焊00366_01未熔合1分割_0_1_非原图.png

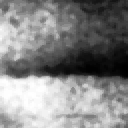
SVMImageClassification/photo/2/补焊00366_01未熔合1分割_0_1_非原图.png
