zrrraa/X-Focus/SVMImageClassification/photo/3/补焊00327_01圆形缺陷9不分割__非原图.png

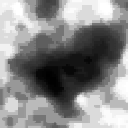
SVMImageClassification/photo/3/补焊00327_01圆形缺陷9不分割__非原图.png
