zrrraa/X-Focus/SVMImageClassification/photo/3/补焊00328_02圆形缺陷1不分割__非原图.png

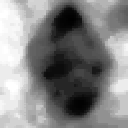
SVMImageClassification/photo/3/补焊00328_02圆形缺陷1不分割__非原图.png
