zrrraa/X-Focus/SVMImageClassification/photo/3/补焊00341_01圆形缺陷2不分割__非原图.png

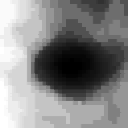
SVMImageClassification/photo/3/补焊00341_01圆形缺陷2不分割__非原图.png
