zrrraa/X-Focus/SVMImageClassification/photo/3/补焊00343_01圆形缺陷20不分割__非原图.png

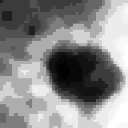
SVMImageClassification/photo/3/补焊00343_01圆形缺陷20不分割__非原图.png
