zrrraa/X-Focus/SVMImageClassification/photo/3/补焊00344_02圆形缺陷8不分割__非原图.png

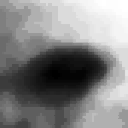
SVMImageClassification/photo/3/补焊00344_02圆形缺陷8不分割__非原图.png
