zrrraa/X-Focus/SVMImageClassification/photo/3/补焊00346_01圆形缺陷3不分割__非原图.png

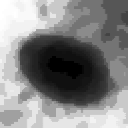
SVMImageClassification/photo/3/补焊00346_01圆形缺陷3不分割__非原图.png
