zrrraa/X-Focus/SVMImageClassification/photo/3/补焊00357_01圆形缺陷10不分割__非原图.png

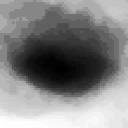
SVMImageClassification/photo/3/补焊00357_01圆形缺陷10不分割__非原图.png
