zrrraa/X-Focus/SVMImageClassification/photo/3/补焊00362_01圆形缺陷7不分割__非原图.png

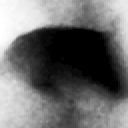
SVMImageClassification/photo/3/补焊00362_01圆形缺陷7不分割__非原图.png
