zrrraa/X-Focus/SVMImageClassification/photo/3/补焊00372_01圆形缺陷5不分割__非原图.png

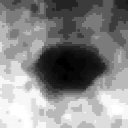
SVMImageClassification/photo/3/补焊00372_01圆形缺陷5不分割__非原图.png
