zrrraa/X-Focus/SVMImageClassification/photo/3/补焊00374_01圆形缺陷1不分割__非原图.png

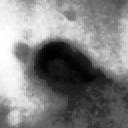
SVMImageClassification/photo/3/补焊00374_01圆形缺陷1不分割__非原图.png
