zrrraa/X-Focus/SVMImageClassification/photo/3/补焊00376_01圆形缺陷4不分割__非原图.png

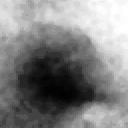
SVMImageClassification/photo/3/补焊00376_01圆形缺陷4不分割__非原图.png
