zrrraa/X-Focus/SVMImageClassification/test_photo/output_image_16.png

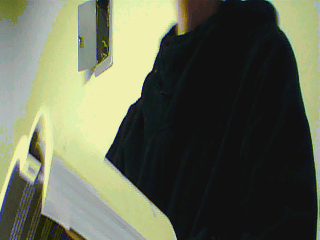
SVMImageClassification/test_photo/output_image_16.png
