zrrraa/X-Focus/SVMImageClassification/test_photo/output_image_17.png

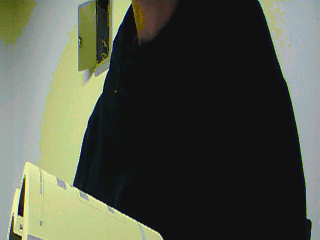
SVMImageClassification/test_photo/output_image_17.png
