zrrraa/X-Focus/SVMImageClassification/test_photo/output_image_18.png

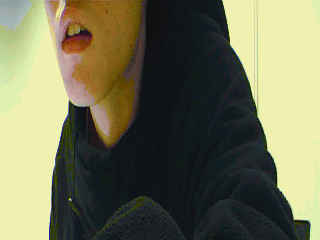
SVMImageClassification/test_photo/output_image_18.png
