zrrraa/X-Focus/SVMImageClassification/test_photo/output_image_19.png

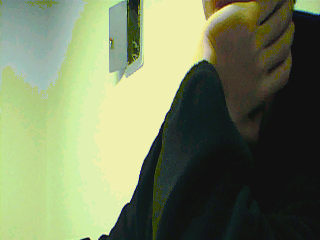
SVMImageClassification/test_photo/output_image_19.png
