zrrraa/X-Focus/arduino/esp-01-IP/config.h

/* configuration settings for project */

// WiFi access point settings
const char* ssid     = "eworks";         // The SSID (name) of the Wi-Fi network you want to connect to
const char* password = "zdkjy221";     // The password of the Wi-Fi network
