zrrraa/X-Focus/test/ov_show_array.py

# Import the needed libraries
from matplotlib import pyplot as plt
import numpy as np
import struct

# Copy the output of the Serial Monitor to the variable below
HEXADECIMAL_BYTES = [0xC343, 0xC343, 0x4433, 0x2133, 0xE031, 0x4521, 0x4721, 0x6721, 0xC731, 0x243, 0xA153, 0xC453, 0xC343, 0x354, 0x321, 0xC422, 0xE522, 0x521, 0x4631, 0x6264, 0x2354, 0x8321, 0x6312, 0xA612, 0x4421, 0xC731, 0xA731, 0x6143, 0x364, 0x354, 0x4654, 0x6454, 0x8621, 0x6412, 0xA622, 0xA622, 0xE741, 0xC731, 0xA243, 0xE453, 0xC453, 0xC353, 0xE453, 0xC443, 0xE453, 0xC443, 0xC343, 0xE453, 0xC453, 0xC453, 0xC443, 0xA343, 0xA343, 0xA353, 0x8343, 0x8343, 0xC453, 0xE353, 0xC443, 0xC443, 0xA343, 0xC343, 0xC343, 0xA343, 0xA343, 0xC343, 0xE343, 0xA333, 0xA143, 0xA143, 0x6343, 0xA143, 0xC343, 0xE453, 0xC443, 0xA343, 0x6443, 0x8343, 0x8343, 0xA343, 0xE443, 0x444, 0xC543, 0xC643, 0x8643, 0x433, 0x6021, 0xE331, 0xA664, 0xC454, 0x6654, 0x2654, 0x654, 0x654, 0xA443, 0xA443, 0x8021, 0xC743, 0xE343, 0x2333, 0x2321, 0xE722, 0x6012, 0xE410, 0xA310, 0x8110, 0x8110, 0xA110, 0x8110, 0x8110, 0xC110, 0xE110, 0x8110, 0x8110, 0x8110, 0x8110, 0x8110, 0x8110, 0x8110, 0x8110, 0x8110, 0x8110, 0x8110, 0x8110, 0x8110, 0x8110, 0x8110, 0x8110, 0x8110, 0x8110, 0x8110, 0x8110, 0x8110, 0x8110, 0x8110, 0x8110, 0x8110, 0x8110, 0x8110, 0x8110, 0x8110, 0xA110, 0xA110, 0xC110, 0xC110, 0xC110, 0xA110, 0x312, 0x312, 0xE110, 0xC110, 0xE310, 0x4322, 0x4322, 0x4422, 0xA322, 0x4531, 0xC731, 0xA031, 0x6031, 0x143, 0x4243, 0x4133, 0x6133, 0x6143, 0x6143, 0x6143, 0x2343, 0x4143, 0x4133, 0x6143, 0x6133, 0x6143, 0x6143, 0x4143, 0x4143, 0x4143, 0x6143, 0x4143, 0x6343, 0x4343, 0x6143, 0x6343, 0x6143, 0xA343, 0xA343, 0xA3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
